vascofazza/cloxie_nixie_clock/nixie_firmware/src/drivers/sensors.cpp

#include "sensors.hpp"

SensorDriver::SensorDriver()
{
  reset_readings();
  pinMode(LIGHT_SENSOR_PIN, INPUT);
  max_brightness = false;
  // Setup a oneWire instance to communicate with any OneWire devices
  onewire_instance = new OneWire(ONE_WIRE_BUS);
  // Pass our oneWire reference to Dallas Temperature sensor
  sensors = new DallasTemperature(onewire_instance);
  sensors->setResolution(9);
  sensors->begin();
  sensors_ticker.attach_ms(ANALOG_READ_INTERVAL, std::bind(&SensorDriver::loop, this));
}

void SensorDriver::loop()
{
  static uint16_t idx = 0;
  int last_reading = max_brightness ? PWMRANGE : analogRead(LIGHT_SENSOR_PIN);
  last_reading = map(last_reading, 0, MAX_LIGHT_READING_VAL, 0, PWMRANGE);
  light_sensor_total -= light_sensor_readings[idx];
  light_sensor_total += last_reading;
  light_sensor_readings[idx] = last_reading;
  idx = (idx + 1) % NUM_OF_READINGS;

#ifdef DEBUG
  static elapsedMillis deb_mils;
  if (deb_mils > 1000)
  {
    DEBUG_PRINT(F("Light sensor averaged reading: "));
    DEBUG_PRINTLN(light_sensor_total / NUM_OF_READINGS + config.brightness_offset);
    deb_mils = 0;
  }
#endif
}

/*
   Smoothing the analogue sensor reading
*/
float SensorDriver::get_light_sensor_reading()
{
  if (!config.adaptive_brightness)
    return DEFAULT_BRIGHTNESS;

  float average_reading = (float)light_sensor_total / NUM_OF_READINGS;
  average_reading += config.brightness_offset;
  return min((float)PWMRANGE, max(0.f, average_reading));
}

void SensorDriver::set_max_brightness(bool val)
{
  this->max_brightness = val;
}

void SensorDriver::feed_readings()
{
  DEBUG_PRINT(F("Feeding sensor..."));
  for (int i = 0; i < NUM_OF_READINGS; i++)
  {
    loop();
    activeDelay(ANALOG_READ_INTERVAL);
  }
  DEBUG_PRINTLN(F("Done."));
}

void SensorDriver::reset_readings()
{
  light_sensor_total = 0;
  for (int i = 0; i < NUM_OF_READINGS; i++)
  {
    light_sensor_readings[i] = 0;
  }
}

float SensorDriver::get_temperature_sensor_reading()
{
  static elapsedMillis reading_interval;
  static float last_temp_reading = -1;

  if (last_temp_reading < 0 || reading_interval > TEMP_READ_INTERVAL)
  {
    DEBUG_PRINT(F("Requesting temperatures..."));
    sensors->requestTemperatures();
    DEBUG_PRINTLN(F("DONE"));
    float temperature_reading = config.celsius ? sensors->getTempCByIndex(0) : sensors->getTempFByIndex(0);
    if (temperature_reading != DEVICE_DISCONNECTED_C)
    {
      last_temp_reading = temperature_reading;
    }
    DEBUG_PRINT(F("Temperature for the device 1 (index 0) is: "));
    DEBUG_PRINTLN(last_temp_reading);
    reading_interval = 0;
  }
  return last_temp_reading;
}
