vascofazza/cloxie_nixie_clock/nixie_firmware/src/drivers/leds_patterns.hpp

#ifndef LEDS_PATTERNS_HPP
#define LEDS_PATTERNS_HPP

#include <FastLED.h>

#if FASTLED_VERSION < 3001000
#error "Requires FastLED 3.1 or later; check github for latest code."
#endif

void solid(CRGB *leds, uint8_t num_leds, int gHue)
{
  fill_rainbow(leds, num_leds, gHue, 0);
}

void lava(CRGB *leds, uint8_t num_leds, int gHue)
{
  // random colored speckles that blink in and fade smoothly
  fadeToBlackBy(leds, num_leds, 10);
  int pos = random16(num_leds);
  leds[pos] = CHSV(gHue + random8(3), 255, 255);
}

void lava_beat(CRGB *leds, uint8_t num_leds, int gHue)
{
  // a colored dot sweeping back and forth, with fading trails
  fadeToBlackBy(leds, num_leds, 5);
  int pos = beatsin16(13, 0, num_leds - 1);
  leds[pos] += CHSV(gHue, 255, 100);
}

void rainbow(CRGB *leds, uint8_t num_leds, int gHue)
{
  // FastLED's built-in rainbow generator
  fill_rainbow(leds, num_leds, gHue, 7);
}

void addGlitter(CRGB *leds, uint8_t num_leds, fract8 chanceOfGlitter)
{
  if (random8() < chanceOfGlitter)
  {
    leds[random16(num_leds)] += CRGB::White;
  }
}

void rainbowWithGlitter(CRGB *leds, uint8_t num_leds, int gHue)
{
  // built-in FastLED rainbow, plus some random sparkly glitter
  rainbow(leds, num_leds, gHue);
  addGlitter(leds, num_leds, 80);
}

void confetti(CRGB *leds, uint8_t num_leds, int gHue)
{
  // random colored speckles that blink in and fade smoothly
  fadeToBlackBy(leds, num_leds, 10);
  int pos = random16(num_leds);
  leds[pos] += CHSV(gHue + random8(64), 200, 255);
}

void sinelon(CRGB *leds, uint8_t num_leds, int gHue)
{
  // a colored dot sweeping back and forth, with fading trails
  fadeToBlackBy(leds, num_leds, 15);
  int pos = beatsin16(30, 0, num_leds - 1);
  leds[pos] += CHSV(gHue, 255, 100);
}

void bpm(CRGB *leds, uint8_t num_leds, int gHue)
{
  // colored stripes pulsing at a defined Beats-Per-Minute (BPM)
  uint8_t BeatsPerMinute = 62;
  CRGBPalette16 palette = PartyColors_p;
  uint8_t beat = beatsin8(BeatsPerMinute, 64, 255);
  for (int i = 0; i < num_leds; i++)
  { //9948
    leds[i] = ColorFromPalette(palette, gHue + (i * 2), beat - gHue + (i * 10));
  }
}

void juggle(CRGB *leds, uint8_t num_leds, int gHue)
{
  // eight colored dots, weaving in and out of sync with each other
  fadeToBlackBy(leds, num_leds, 20);
  byte dothue = 0;
  for (int i = 0; i < 8; i++)
  {
    leds[beatsin16(i + 7, 0, num_leds - 1)] |= CHSV(dothue, 200, 255);
    dothue += 32;
  }
}

void pride(CRGB *leds, uint8_t num_leds, int gHue)
{
  static uint16_t sPseudotime = 0;
  static uint16_t sLastMillis = 0;
  static uint16_t sHue16 = 0;

  uint8_t sat8 = beatsin88(87, 220, 250);
  uint8_t brightdepth = beatsin88(341, 96, 224);
  uint16_t brightnessthetainc16 = beatsin88(203, (25 * 256), (40 * 256));
  uint8_t msmultiplier = beatsin88(147, 23, 60);

  uint16_t hue16 = sHue16; //gHue * 256;
  uint16_t hueinc16 = beatsin88(113, 1, 3000);

  uint16_t ms = millis();
  uint16_t deltams = ms - sLastMillis;
  sLastMillis = ms;
  sPseudotime += deltams * msmultiplier;
  sHue16 += deltams * beatsin88(400, 5, 9);
  uint16_t brightnesstheta16 = sPseudotime;

  for (uint16_t i = 0; i < NUM_LEDS; i++)
  {
    hue16 += hueinc16;
    uint8_t hue8 = hue16 / 256;

    brightnesstheta16 += brightnessthetainc16;
    uint16_t b16 = sin16(brightnesstheta16) + 32768;

    uint16_t bri16 = (uint32_t)((uint32_t)b16 * (uint32_t)b16) / 65536;
    uint8_t bri8 = (uint32_t)(((uint32_t)bri16) * brightdepth) / 65536;
    bri8 += (255 - brightdepth);

    CRGB newcolor = CHSV(hue8, sat8, bri8);

    uint16_t pixelnumber = i;
    pixelnumber = (NUM_LEDS - 1) - pixelnumber;

    nblend(leds[pixelnumber], newcolor, 64);
  }
}

void pulse(CRGB *leds, uint8_t num_leds, int gHue)
{
  // colored stripes pulsing at a defined Beats-Per-Minute (BPM)
  uint8_t BeatsPerMinute = 30;
  uint8_t beat = beatsin8(BeatsPerMinute, 64, 255);
  for (int i = 0; i < num_leds; i++)
  {
    leds[i] = CHSV(gHue, 255, beat);
  }
}

#define COOLING 55

// SPARKING: What chance (out of 255) is there that a new spark will be lit?
// Higher chance = more roaring fire.  Lower chance = more flickery fire.
// Default 120, suggested range 50-200.
#define SPARKING 120

void fire(CRGB *leds, uint8_t num_leds, int gHue)
{
  // Array of temperature readings at each simulation cell
  static byte heat[NUM_LEDS];

  // Step 1.  Cool down every cell a little
  for (int i = 0; i < NUM_LEDS; i++)
  {
    heat[i] = qsub8(heat[i], random8(0, ((COOLING * 10) / NUM_LEDS) + 2));
  }

  // Step 2.  Heat from each cell drifts 'up' and diffuses a little
  for (int k = NUM_LEDS - 1; k >= 2; k--)
  {
    heat[k] = (heat[k - 1] + heat[k - 2] + heat[k - 2]) / 3;
  }

  // Step 3.  Randomly ignite new 'sparks' of heat near the bottom
  if (random8() < SPARKING)
  {
    int y = random8(7);
    heat[y] = qadd8(heat[y], random8(160, 255));
  }

  // Step 4.  Map from heat cells to LED colors
  for (int j = 0; j < NUM_LEDS; j++)
  {
    CRGB color = HeatColor(heat[j]);
    int pixelnumber;
    pixelnumber = j;
    leds[pixelnumber] = color;
  }
}

CRGBPalette16 pacifica_palette_1 =
    {0x000507, 0x000409, 0x00030B, 0x00030D, 0x000210, 0x000212, 0x000114, 0x000117,
     0x000019, 0x00001C, 0x000026, 0x000031, 0x00003B, 0x000046, 0x14554B, 0x28AA50};
CRGBPalette16 pacifica_palette_2 =
    {0x000507, 0x000409, 0x00030B, 0x00030D, 0x000210, 0x000212, 0x000114, 0x000117,
     0x000019, 0x00001C, 0x000026, 0x000031, 0x00003B, 0x000046, 0x0C5F52, 0x19BE5F};
CRGBPalette16 pacifica_palette_3 =
    {0x000208, 0x00030E, 0x000514, 0x00061A, 0x000820, 0x000927, 0x000B2D, 0x000C33,
     0x000E39, 0x001040, 0x001450, 0x001860, 0x001C70, 0x002080, 0x1040BF, 0x2060FF};

// Add one layer of waves into the led array
void pacifica_one_layer(CRGB *leds, CRGBPalette16 &p, uint16_t cistart, uint16_t wavescale, uint8_t bri, uint16_t ioff)
{
  uint16_t ci = cistart;
  uint16_t waveangle = ioff;
  uint16_t wavescale_half = (wavescale / 2) + 20;
  for (uint16_t i = 0; i < NUM_LEDS; i++)
  {
    waveangle += 250;
    uint16_t s16 = sin16(waveangle) + 32768;
    uint16_t cs = scale16(s16, wavescale_half) + wavescale_half;
    ci += cs;
    uint16_t sindex16 = sin16(ci) + 32768;
    uint8_t sindex8 = scale16(sindex16, 240);
    CRGB c = ColorFromPalette(p, sindex8, bri, LINEARBLEND);
    leds[i] += c;
  }
}

// Add extra 'white' to areas where the four layers of light have lined up brightly
void pacifica_add_whitecaps(CRGB *leds)
{
  uint8_t basethreshold = beatsin8(9, 55, 65);
  uint8_t wave = beat8(7);

  for (uint16_t i = 0; i < NUM_LEDS; i++)
  {
    uint8_t threshold = scale8(sin8(wave), 20) + basethreshold;
    wave += 7;
    uint8_t l = leds[i].getAverageLight();
    if (l > threshold)
    {
      uint8_t overage = l - threshold;
      uint8_t overage2 = qadd8(overage, overage);
      leds[i] += CRGB(overage, overage2, qadd8(overage2, overage2));
    }
  }
}

// Deepen the blues and greens
void pacifica_deepen_colors(CRGB *leds)
{
  for (uint16_t i = 0; i < NUM_LEDS; i++)
  {
    leds[i].blue = scale8(leds[i].blue, 145);
    leds[i].green = scale8(leds[i].green, 200);
    leds[i] |= CRGB(2, 5, 7);
  }
}

void pacifica(CRGB *leds, uint8_t num_leds, int gHue)
{
  // Increment the four "color index start" counters, one for each wave layer.
  // Each is incremented at a different speed, and the speeds vary over time.
  static uint16_t sCIStart1, sCIStart2, sCIStart3, sCIStart4;
  static uint32_t sLastms = 0;
  uint32_t ms = GET_MILLIS();
  uint32_t deltams = ms - sLastms;
  sLastms = ms;
  uint16_t speedfactor1 = beatsin16(3, 179, 269);
  uint16_t speedfactor2 = beatsin16(4, 179, 269);
  uint32_t deltams1 = (deltams * speedfactor1) / 256;
  uint32_t deltams2 = (deltams * speedfactor2) / 256;
  uint32_t deltams21 = (deltams1 + deltams2) / 2;
  sCIStart1 += (deltams1 * beatsin88(1011, 10, 13));
  sCIStart2 -= (deltams21 * beatsin88(777, 8, 11));
  sCIStart3 -= (deltams1 * beatsin88(501, 5, 7));
  sCIStart4 -= (deltams2 * beatsin88(257, 4, 6));

  // Clear out the LED array to a dim background blue-green
  fill_solid(leds, NUM_LEDS, CRGB(2, 6, 10));

  // Render each of four layers, with different scales and speeds, that vary over time
  pacifica_one_layer(leds, pacifica_palette_1, sCIStart1, beatsin16(3, 11 * 256, 14 * 256), beatsin8(10, 70, 130), 0 - beat16(301));
  pacifica_one_layer(leds, pacifica_palette_2, sCIStart2, beatsin16(4, 6 * 256, 9 * 256), beatsin8(17, 40, 80), beat16(401));
  pacifica_one_layer(leds, pacifica_palette_3, sCIStart3, 6 * 256, beatsin8(9, 10, 38), 0 - beat16(503));
  pacifica_one_layer(leds, pacifica_palette_3, sCIStart4, 5 * 256, beatsin8(8, 10, 28), beat16(601));

  // Add brighter 'whitecaps' where the waves lines up more
  pacifica_add_whitecaps(leds);

  // Deepen the blues and greens a bit
  pacifica_deepen_colors(leds);
}

#endif
