vascofazza/cloxie_nixie_clock/nixie_firmware/src/drivers/clock.cpp

#include "clock.hpp"
#include "blink_patterns.hpp"

BlinkPatternList blink_patterns = {no_blink, static_blink, double_static_blink, fade_out_blink, static_on};

ClockDriver::ClockDriver(TubeDriver *tube_driver)
{
  this->tube_driver = tube_driver;
  display_time = false;
  display_date = false;
  display_timer = false;
  display_stopwatch = false;
  ntpClock.setup();
  systemClock = new SystemClockLoop((Clock *)&ntpClock /*reference*/, nullptr /*backup*/);
  systemClock->setup();
  systemClock->setNow(0);
  blinking = false;
  timer_running = false;
  stopwatch_running = false;
  timer_duration = -1;
  current_timer_value = 0;
  current_stopwatch_value = 0;
  stopwatch_value = 0;
  clock_ticker.attach(1.f, std::bind(&SystemClockLoop::getNow, systemClock));
}

void ClockDriver::loop()
{
  static acetime_t prevNow = systemClock->getNow();
  systemClock->loop();
  acetime_t now = systemClock->getNow();

  ace_time::ZonedDateTime current_time = get_current_time();

  if (display_timer || display_stopwatch)
  {
    if (timer_running || stopwatch_running)
    {
      blink_dots(double_static_blink);
    }
    else if (is_timer_set() || is_stopwatch_set())
    {
      blink_dots(static_blink);
    }
    else
    {
      blink_dots(static_on);
    }
    print_timer_stopwatch();
  }
  else if (display_time)
  {
    blink_dots(blink_patterns[config.blink_mode]);
    print_current_time(current_time);
  }
  else if (display_date)
  {
    print_current_date(current_time);
  }

  if (now - prevNow >= 1)
  {
    blinking = true;
    prevNow = now;
#ifdef DEBUG
    current_time.printTo(Serial);
    Serial.println();
#endif
  }
}

ace_time::ZonedDateTime ClockDriver::get_current_time()
{
  acetime_t now = systemClock->getNow();

  auto time_zone = TimeZone::forZoneInfo(zonedb::kZoneRegistry[config.timezone], &zoneProcessor);
  auto current_time = ZonedDateTime::forEpochSeconds(now, time_zone);
  return current_time;
}

void ClockDriver::blink_dots(void (*pattern)(TubeDriver *, bool, elapsedMillis *))
{
  static elapsedMillis elapsed;
  pattern(tube_driver, blinking, &elapsed);
  blinking = false;
}

void ClockDriver::print_current_time(ace_time::ZonedDateTime current_time)
{
  auto hour = current_time.hour();
  if (!config.h24)
  {
    hour %= 12;
  }
  tube_driver->display_time_and_date(hour, current_time.minute(), current_time.second(), false);
}

void ClockDriver::print_current_date(ace_time::ZonedDateTime current_time)
{
  auto day = current_time.day();
  auto month = current_time.month();
  auto year = current_time.yearTiny();

  tube_driver->display_time_and_date(day, month, year, true);
  tube_driver->set_dots_brightness(PWMRANGE, PWMRANGE);
}

bool ClockDriver::is_night_hours()
{
  auto curr_time = get_current_time();
  int hour = curr_time.hour();
  int sleep_hour = config.sleep_hour;
  int wake_hour = config.wake_hour;
  if (sleep_hour > wake_hour)
  {
    int offset = 24 - sleep_hour;
    sleep_hour = 0;
    wake_hour += offset;
    hour = (hour + offset) % 24;
  }
  return hour >= sleep_hour && hour < wake_hour;
}

void ClockDriver::print_timer_stopwatch()
{
  long val = 0;
  if (display_timer)
  {
    val = timer_running ? timer_duration - (long)current_timer_value : timer_duration;
    if (val <= 0)
      reset_timer();
  }
  else if (display_stopwatch)
  {
    if (stopwatch_running)
    {
      auto mills = millis();
      current_stopwatch_value += mills - stopwatch_value;
      stopwatch_value = mills;
    }
    val = current_stopwatch_value;
    if (val >= 59 + 60 * 60 + 23 * 3600 * 1000)
      reset_stopwatch();
  }

  unsigned long durCS = (val % 1000) / 10;    //Cent-seconds
  unsigned long durSS = (val / 1000) % 60;    //Seconds
  unsigned long durMM = (val / (60000)) % 60; //Minutes
  unsigned long durHH = (val / (3600000));    //Hours
  durHH = durHH % 24;

  if (durHH > 0)
  {
    tube_driver->display_time_and_date(durHH, durMM, durSS, true);
  }
  else
  {
    tube_driver->display_time_and_date(durMM, durSS, durCS, true);
  }
}

void ClockDriver::show_time(bool show)
{
  display_time = show;
  if (show)
  {
    show_date(false);
    show_timer(false);
    show_stopwatch(false);
  }
}

void ClockDriver::show_date(bool show)
{
  display_date = show;
  if (show)
  {
    show_time(false);
    show_timer(false);
    show_stopwatch(false);
  }
}

void ClockDriver::show_timer(bool show)
{
  display_timer = show;
  if (show)
  {
    show_time(false);
    show_date(false);
    show_stopwatch(false);
  }
}

void ClockDriver::show_stopwatch(bool show)
{
  display_stopwatch = show;
  if (show)
  {
    show_time(false);
    show_timer(false);
    show_date(false);
  }
}

void ClockDriver::start_timer(long duration)
{
  if (duration > 0)
  {
    timer_duration = duration;
    timer_running = true;
    current_timer_value = 0;
  }
  else
  {
    if (is_timer_set())
    {
      timer_running = true;
      current_timer_value = 0;
    }
  }
}

void ClockDriver::stop_timer()
{
  timer_running = false;
  timer_duration = max(timer_duration - (long)current_timer_value, 0L);
}

void ClockDriver::reset_timer()
{
  timer_running = false;
  timer_duration = -1;
}

void ClockDriver::start_stopwatch()
{
  if (!is_stopwatch_set())
  {
    current_stopwatch_value = 0;
  }
  stopwatch_value = millis();
  stopwatch_running = true;
}

void ClockDriver::stop_stopwatch()
{
  stopwatch_running = false;
}

void ClockDriver::reset_stopwatch()
{
  stopwatch_running = false;
  stopwatch_value = -1;
  current_stopwatch_value = 0;
}

bool ClockDriver::is_timer_set()
{
  return timer_duration > 0;
}

bool ClockDriver::is_stopwatch_set()
{
  return current_stopwatch_value > 0;
}

bool ClockDriver::is_timer_running()
{
  return timer_running;
}

bool ClockDriver::is_stopwatch_running()
{
  return stopwatch_running;
}

void ClockDriver::set_alarm(long epoch)
{
  acetime_t now = systemClock->getNow();
  auto target = epoch - now;
  start_timer(target);
}
